belenseptian/RS485LP/1.png

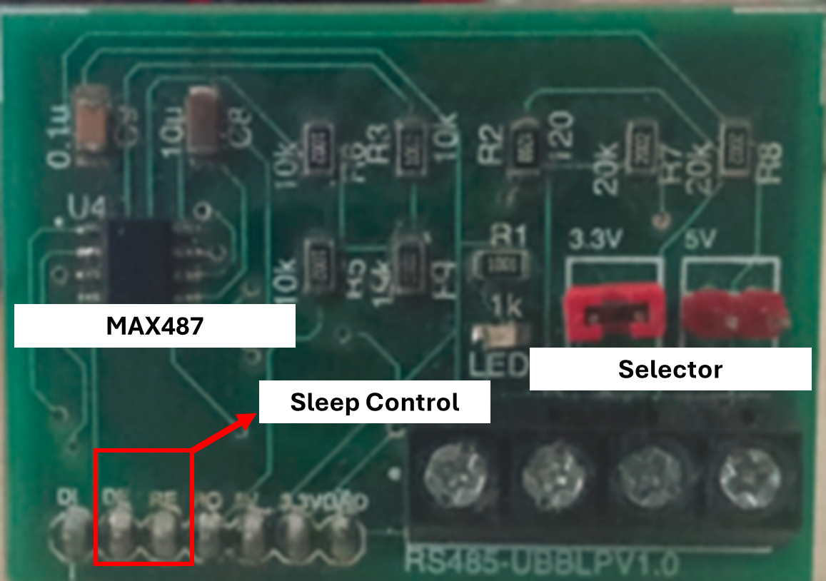
1.png
