belenseptian/RS485LP/2.png

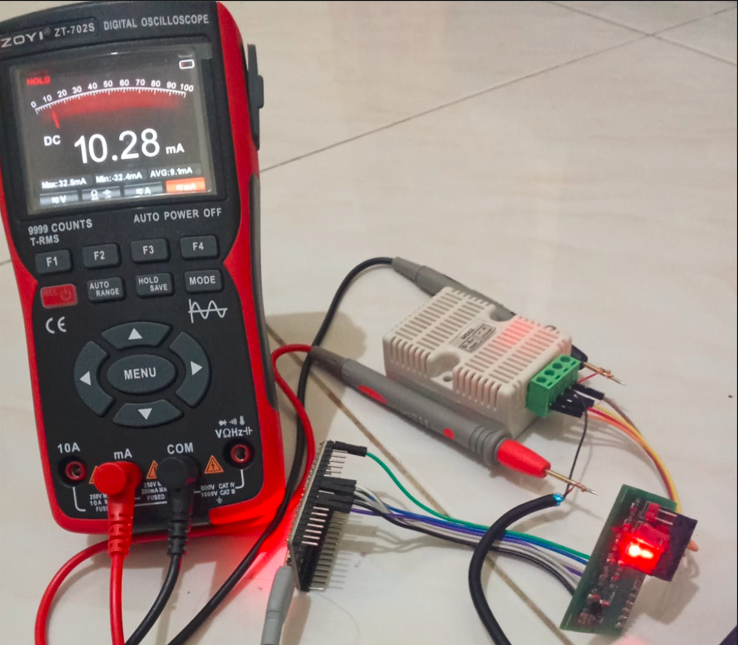
2.png
