belenseptian/RS485LP/3.png

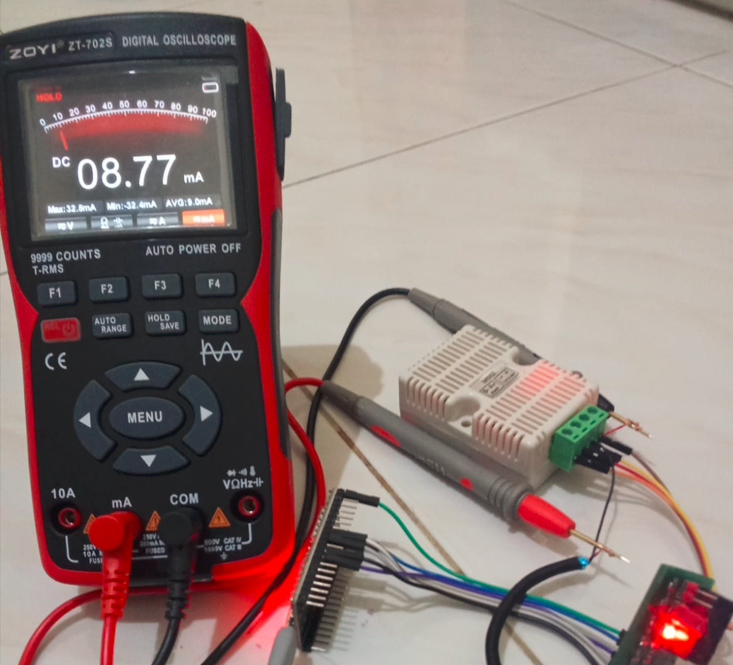
3.png
