belenseptian/RS485LP/4.png

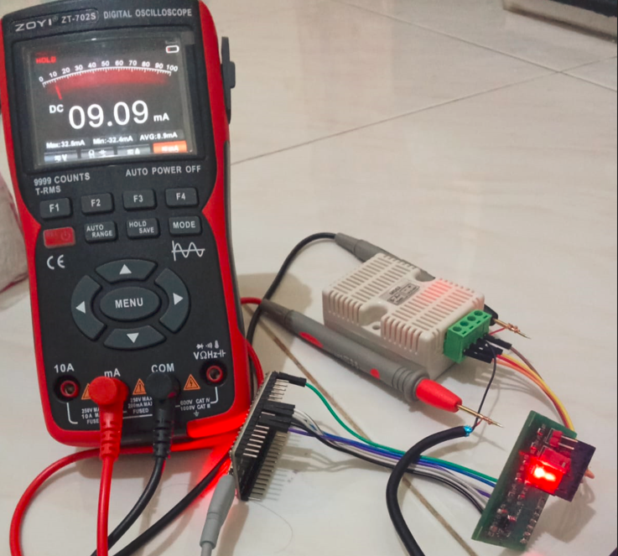
4.png
