belenseptian/RS485LP/5.png

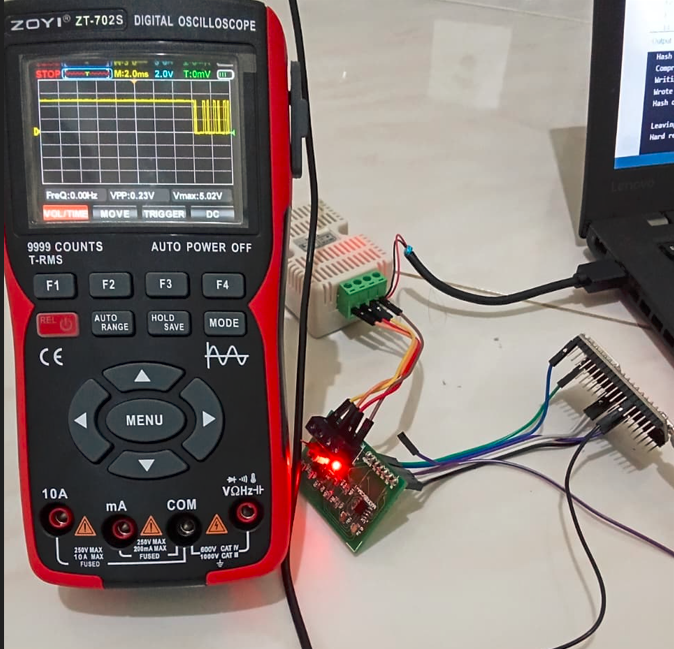
5.png
